daskals/4-PAM-Modulation-of-Ambient-FM-Backscattering-for-Spectrally-Efficient-Low-Power-Applications/Publication_files/Figures/Fig7-eps-converted-to.pdf

10 00 10 00 10
00 01 01 11 10 00 11

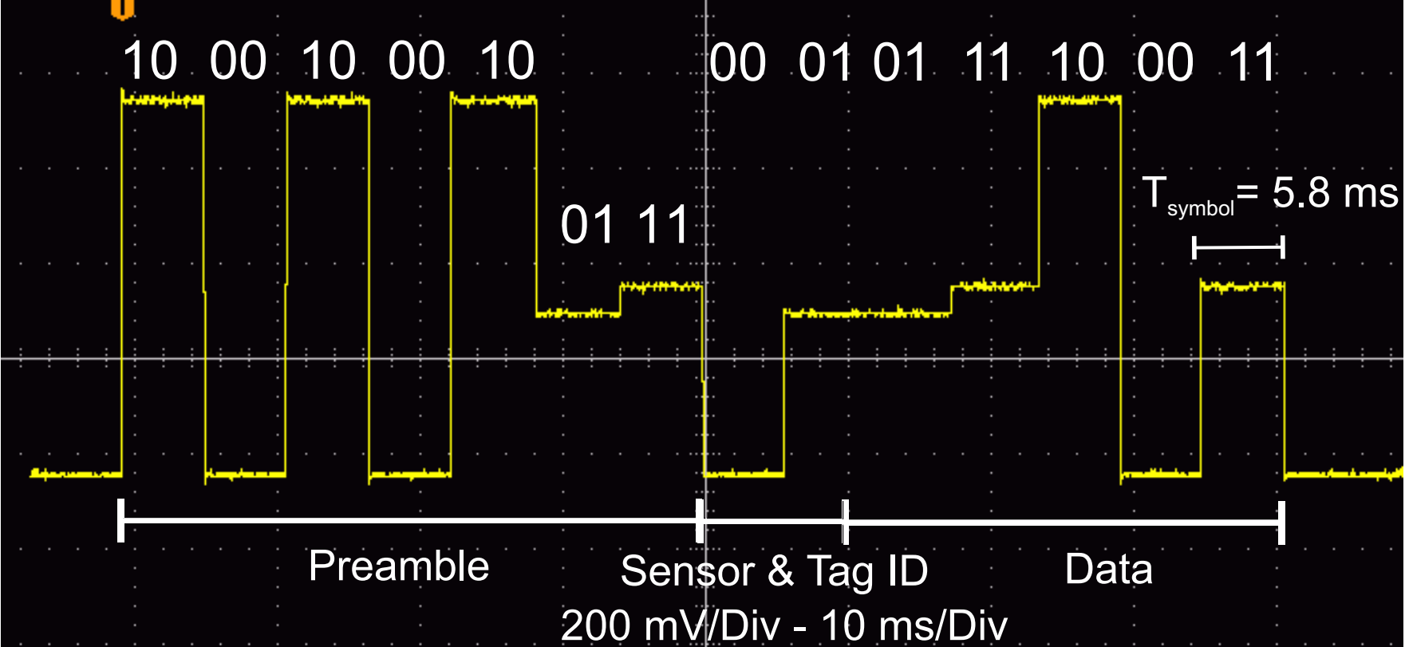
[picture p10: page 1]

T | = 5.8 ms symbol
2 | mV/Div - 10 ms/Div 00

01 11

Preamble | Sensor & Tag ID | Data
