daskals/4-PAM-Modulation-of-Ambient-FM-Backscattering-for-Spectrally-Efficient-Low-Power-Applications/Publication_files/Figures/Fig9-eps-converted-to.pdf

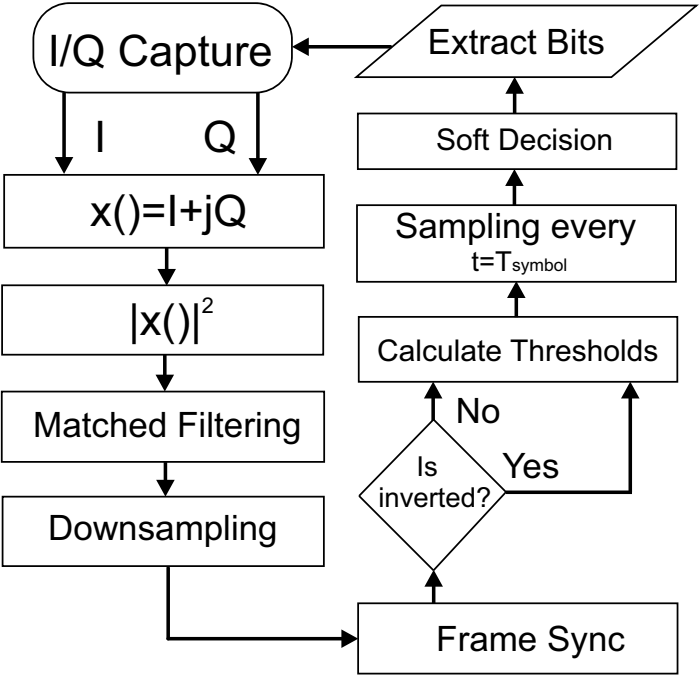
[picture p11: figure]
I/Q Capture; Matched Filtering; Downsampling; Frame Sync; Sampling every; t=Tsymbol; Soft Decision; Extract Bits; Is inverted?; Yes; Calculate Thresholds
