daskals/4-PAM-Modulation-of-Ambient-FM-Backscattering-for-Spectrally-Efficient-Low-Power-Applications/Publication_files/Figures/Fig8-eps-converted-to.pdf

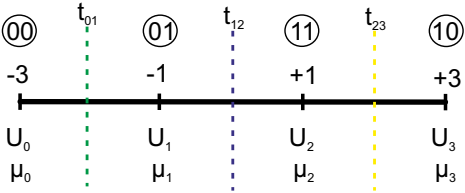
[picture p13: figure]
